bionik/esp32controller/firmware/src/credentials.example.h

#ifndef CREDENTIALS_H
#define CREDENTIALS_H

// Copy this file to credentials.h and fill in your actual credentials, 
// or change defaults in main.cpp if you prefer not to use a separate file.  

// WiFi Credentials
#define WIFI_SSID "your_wifi_network_name"
#define WIFI_PASSWORD "your_wifi_password"

// OTA Credentials
#define OTA_USERNAME "admin"
#define OTA_PASSWORD "change_this_password"

#endif // CREDENTIALS_H
